Cushychicken/bfunc/sw_rtl/source/sin_rom.v

module sin_rom(
    clock,
    phase_in,
    sin_out,
);

// Input Ports
input clock;
input [11:0] phase_in;

// Output Ports
output [9:0] sin_out;

// Internal Ports
integer i;
reg [9:0] sine [0:4095];

initial begin
    sine[0]=0;
    sine[1]=1;
    sine[2]=3;
    sine[3]=4;
    sine[4]=6;
    sine[5]=7;
    sine[6]=9;
    sine[7]=10;
    sine[8]=12;
    sine[9]=14;
    sine[10]=15;
    sine[11]=17;
    sine[12]=18;
    sine[13]=20;
    sine[14]=21;
    sine[15]=23;
    sine[16]=25;
    sine[17]=26;
    sine[18]=28;
    sine[19]=29;
    sine[20]=31;
    sine[21]=32;
    sine[22]=34;
    sine[23]=36;
    sine[24]=37;
    sine[25]=39;
    sine[26]=40;
    sine[27]=42;
    sine[28]=43;
    sine[29]=45;
    sine[30]=47;
    sine[31]=48;
    sine[32]=50;
    sine[33]=51;
    sine[34]=53;
    sine[35]=54;
    sine[36]=56;
    sine[37]=58;
    sine[38]=59;
    sine[39]=61;
    sine[40]=62;
    sine[41]=64;
    sine[42]=65;
    sine[43]=67;
    sine[44]=69;
    sine[45]=70;
    sine[46]=72;
    sine[47]=73;
    sine[48]=75;
    sine[49]=76;
    sine[50]=78;
    sine[51]=80;
    sine[52]=81;
    sine[53]=83;
    sine[54]=84;
    sine[55]=86;
    sine[56]=87;
    sine[57]=89;
    sine[58]=90;
    sine[59]=92;
    sine[60]=94;
    sine[61]=95;
    sine[62]=97;
    sine[63]=98;
    sine[64]=100;
    sine[65]=101;
    sine[66]=103;
    sine[67]=105;
    sine[68]=106;
    sine[69]=108;
    sine[70]=109;
    sine[71]=111;
    sine[72]=112;
    sine[73]=114;
    sine[74]=115;
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
    sine[4086]=-15;
    sine[4087]=-14;
    sine[4088]=-12;
    sine[4089]=-10;
    sine[4090]=-9;
    sine[4091]=-7;
    sine[4092]=-6;
    sine[4093]=-4;
    sine[4094]=-3;
    sine[4095]=-1;
end 

// ROM Logic
always @(posedge clock) begin 
    sin_out = sine[phase_in];
end

endmodule
